dcpedit/mission-control/pcb/pcb.kicad_sch

## KiCad design pcb/pcb.kicad_sch (2024-04-23)

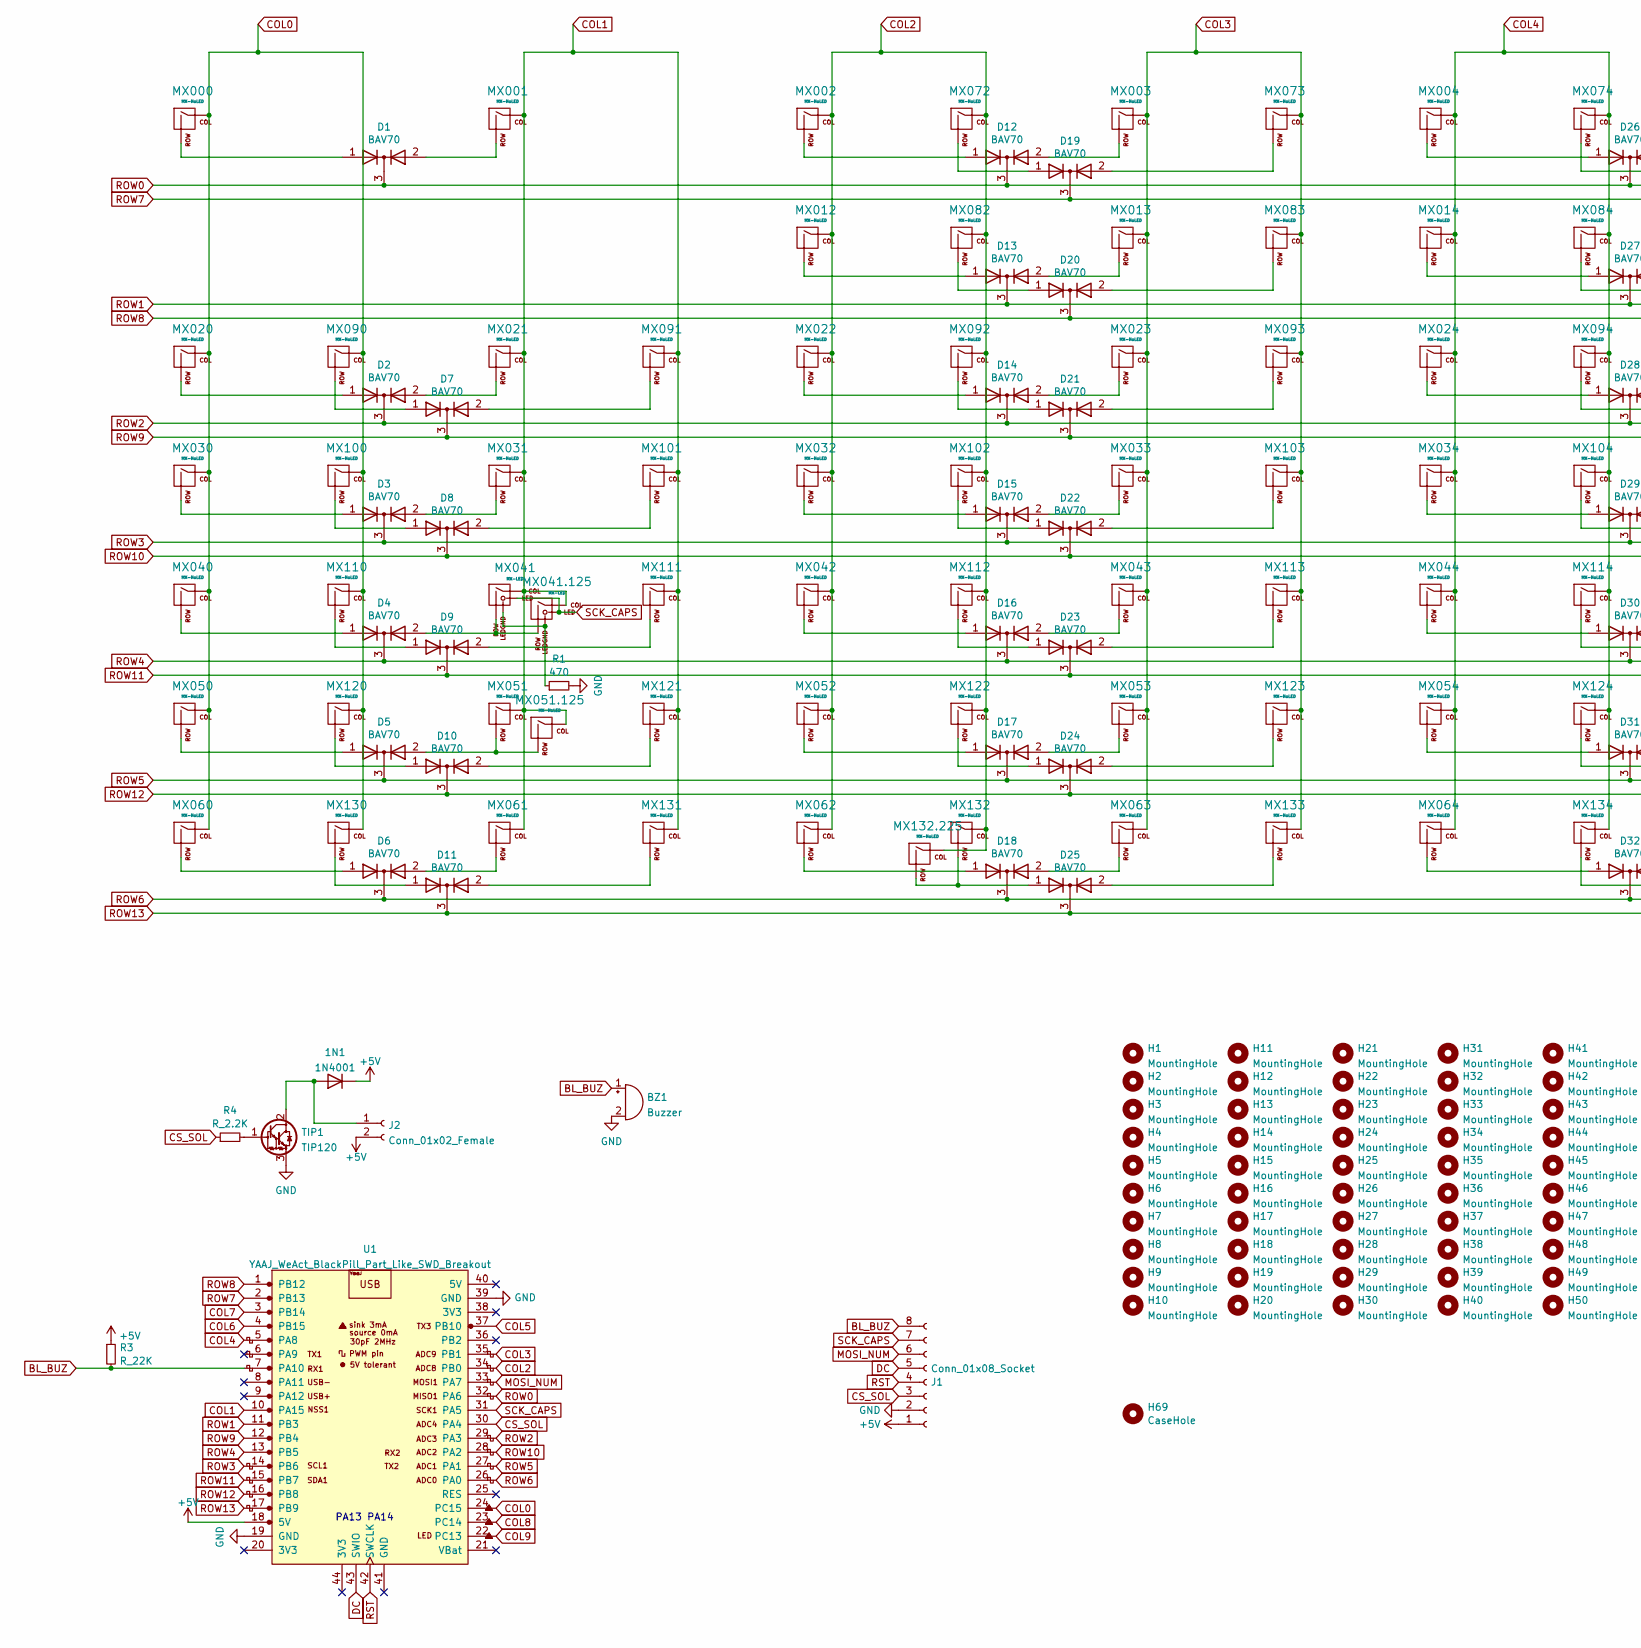
[picture p4: schematic pcb.kicad_sch, part in row 1, column 1]

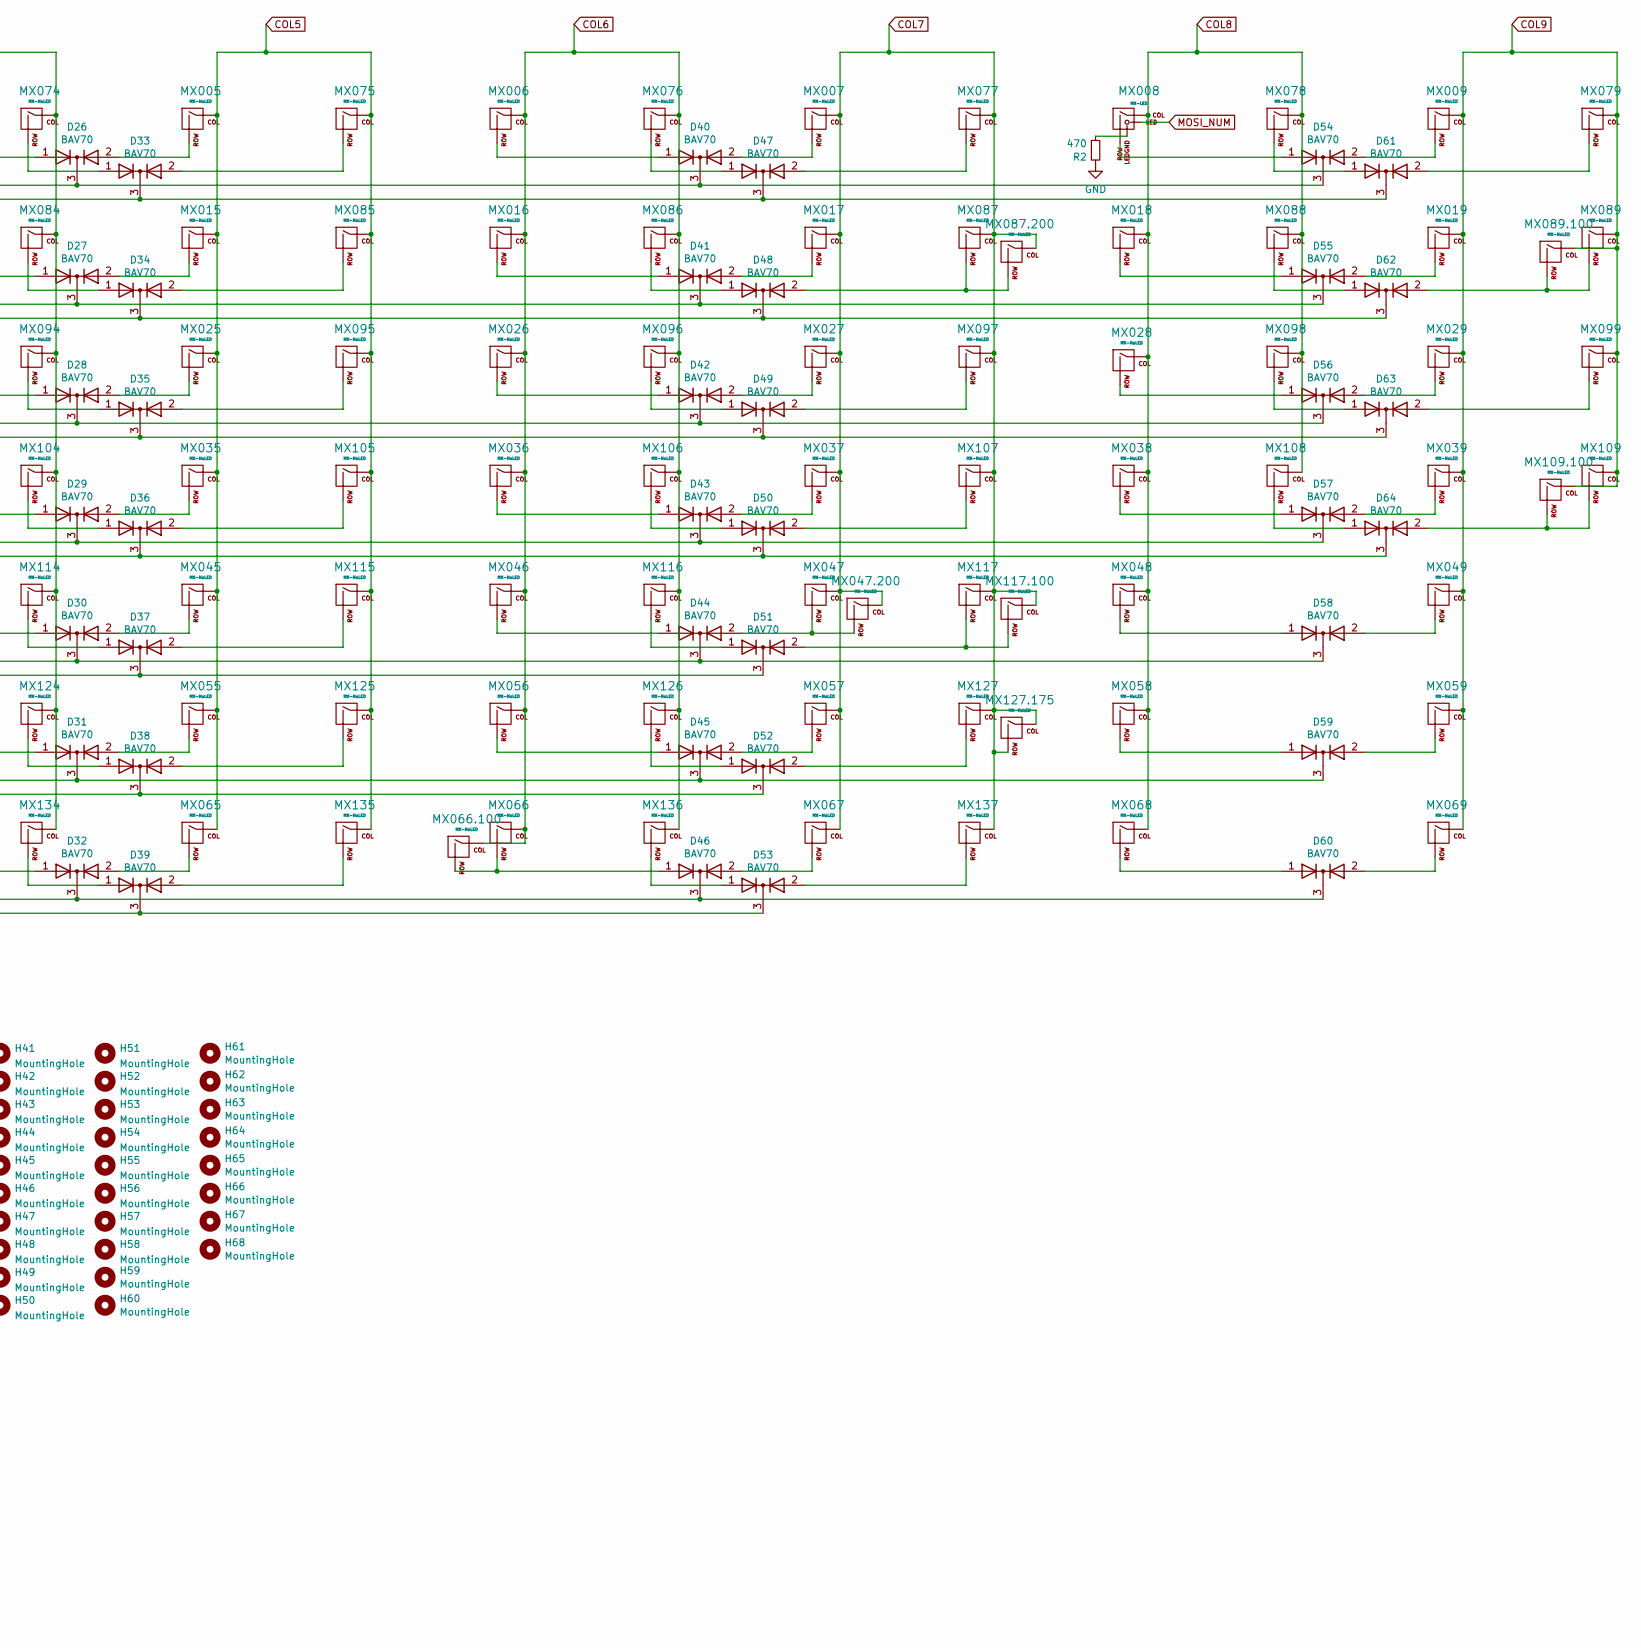
[picture p5: schematic pcb.kicad_sch, part in row 1, column 2]

Parts:
1N1: 1N4001; D_DO-41_SOD81_P10.16mm_Horizontal
BZ1: Buzzer
D1, D2, D3, D4, D5, D6, D7, D8, D9, D10, D11, D12, D13, D14, D15, D16, D17, D18, D19, D20, D21, D22, D23, D24, D25, D26, D27, D28, D29, D30, D31, D32, D33, D34, D35, D36, D37, D38, D39, D40, D41, D42, D43, D44, D45, D46, D47, D48, D49, D50, D51, D52, D53, D54, D55, D56, D57, D58, D59, D60, D61, D62, D63, D64: BAV70; SOT-23_Handsoldering
H1, H2, H3, H4, H5, H6, H7, H8, H9, H10, H11, H12, H13, H14, H15, H16, H17, H18, H19, H20, H21, H22, H23, H24, H25, H26, H27, H28, H29, H30, H31, H32, H33, H34, H35, H36, H37, H38, H39, H40, H41, H42, H43, H44, H45, H46, H47, H48, H49, H50, H51, H52, H53, H54, H55, H56, H57, H58, H59, H60, H61, H62, H63, H64, H65, H66, H67, H68: MountingHole
H69: CaseHole
J1: Conn_01x08_Socket
J2: Conn_01x02_Female; PinHeader_1x02_P2.54mm_Vertical
MX000, MX001, MX002, MX003, MX004, MX005, MX006, MX007, MX009, MX012, MX013, MX014, MX015, MX016, MX017, MX018, MX019, MX020, MX021, MX022, MX023, MX024, MX025, MX026, MX027, MX028, MX029, MX030, MX031, MX032, MX033, MX034, MX035, MX036, MX037, MX038, MX039, MX040, MX042, MX043, MX044, MX045, MX046, MX047, MX047.200, MX048, MX049, MX050, MX051, MX051.125, MX052, MX053, MX054, MX055, MX056, MX057, MX058, MX059, MX060, MX061, MX062, MX063, MX064, MX065, MX066, MX066.100, MX067, MX068, MX069, MX072, MX073, MX074, MX075, MX076, MX077, MX078, MX079, MX082, MX083, MX084, MX085, MX086, MX087, MX087.200, MX088, MX089, MX089.100, MX090, MX091, MX092, MX093, MX094, MX095, MX096, MX097, MX098, MX099, MX100, MX101, MX102, MX103, MX104, MX105, MX106, MX107, MX108, MX109, MX109.100, MX110, MX111, MX112, MX113, MX114, MX115, MX116, MX117, MX117.100, MX120, MX121, MX122, MX123, MX124, MX125, MX126, MX127, MX127.175, MX130, MX131, MX132, MX132.225, MX133, MX134, MX135, MX136, MX137: MX-NoLED; MXOnly-1U-NoLED
MX008, MX041, MX041.125: MX-LED
R1, R2: 470
R3: R_22K; Resistor
R4: R_2.2K; Resistor
TIP1: TIP120; TO-220-3_Vertical
U1: YAAJ_WeAct_BlackPill_Part_Like_SWD_Breakout; YAAJ_WeAct_BlackPill_SWD_2

Connections:
+5V: 1N1.1 (K), J1.1, J2.2, R3.1, U1.18 (5V)
BL_BUZ: BZ1.1 (-), J1.8, R3.2, U1.7 (PA10)
COL0: MX000.1 (COL), MX020.1 (COL), MX030.1 (COL), MX040.1 (COL), MX050.1 (COL), MX060.1 (COL), MX090.1 (COL), MX100.1 (COL), MX110.1 (COL), MX120.1 (COL), MX130.1 (COL), U1.24 (PC15)
COL1: MX001.1 (COL), MX021.1 (COL), MX031.1 (COL), MX041.1 (COL), MX041.125.1 (COL), MX051.1 (COL), MX051.125.1 (COL), MX061.1 (COL), MX091.1 (COL), MX101.1 (COL), MX111.1 (COL), MX121.1 (COL), MX131.1 (COL), U1.10 (PA15)
COL2: MX002.1 (COL), MX012.1 (COL), MX022.1 (COL), MX032.1 (COL), MX042.1 (COL), MX052.1 (COL), MX062.1 (COL), MX072.1 (COL), MX082.1 (COL), MX092.1 (COL), MX102.1 (COL), MX112.1 (COL), MX122.1 (COL), MX132.1 (COL), MX132.225.1 (COL), U1.34 (PB0)
COL3: MX003.1 (COL), MX013.1 (COL), MX023.1 (COL), MX033.1 (COL), MX043.1 (COL), MX053.1 (COL), MX063.1 (COL), MX073.1 (COL), MX083.1 (COL), MX093.1 (COL), MX103.1 (COL), MX113.1 (COL), MX123.1 (COL), MX133.1 (COL), U1.35 (PB1)
COL4: MX004.1 (COL), MX014.1 (COL), MX024.1 (COL), MX034.1 (COL), MX044.1 (COL), MX054.1 (COL), MX064.1 (COL), MX074.1 (COL), MX084.1 (COL), MX094.1 (COL), MX104.1 (COL), MX114.1 (COL), MX124.1 (COL), MX134.1 (COL), U1.5 (PA8)
COL5: MX005.1 (COL), MX015.1 (COL), MX025.1 (COL), MX035.1 (COL), MX045.1 (COL), MX055.1 (COL), MX065.1 (COL), MX075.1 (COL), MX085.1 (COL), MX095.1 (COL), MX105.1 (COL), MX115.1 (COL), MX125.1 (COL), MX135.1 (COL), U1.37 (PB10)
COL6: MX006.1 (COL), MX016.1 (COL), MX026.1 (COL), MX036.1 (COL), MX046.1 (COL), MX056.1 (COL), MX066.1 (COL), MX066.100.1 (COL), MX076.1 (COL), MX086.1 (COL), MX096.1 (COL), MX106.1 (COL), MX116.1 (COL), MX126.1 (COL), MX136.1 (COL), U1.4 (PB15)
COL7: MX007.1 (COL), MX017.1 (COL), MX027.1 (COL), MX037.1 (COL), MX047.1 (COL), MX047.200.1 (COL), MX057.1 (COL), MX067.1 (COL), MX077.1 (COL), MX087.1 (COL), MX087.200.1 (COL), MX097.1 (COL), MX107.1 (COL), MX117.1 (COL), MX117.100.1 (COL), MX127.1 (COL), MX127.175.1 (COL), MX127.175.2 (ROW), MX137.1 (COL), U1.3 (PB14)
COL8: MX008.1 (COL), MX018.1 (COL), MX028.1 (COL), MX038.1 (COL), MX048.1 (COL), MX058.1 (COL), MX068.1 (COL), MX078.1 (COL), MX088.1 (COL), MX098.1 (COL), MX108.1 (COL), U1.23 (PC14)
COL9: MX009.1 (COL), MX019.1 (COL), MX029.1 (COL), MX039.1 (COL), MX049.1 (COL), MX059.1 (COL), MX069.1 (COL), MX079.1 (COL), MX089.1 (COL), MX089.100.1 (COL), MX099.1 (COL), MX109.1 (COL), MX109.100.1 (COL), U1.22 (PC13)
CS_SOL: J1.3, R4.1, U1.30 (PA4)
DC: J1.5, U1.43 (SWIO)
GND: BZ1.2 (+), J1.2, R1.2, R2.2, TIP1.3 (E), U1.19 (GND), U1.39 (GND)
MOSI_NUM: J1.6, MX008.3 (LED), U1.33 (PA7)
unnamed: 1N1.2 (A), J2.1, TIP1.2 (C)
unnamed: D1.1 (A), MX000.2 (ROW)
unnamed: D1.2 (A), MX001.2 (ROW)
unnamed: D2.1 (A), MX020.2 (ROW)
unnamed: D2.2 (A), MX021.2 (ROW)
unnamed: D3.1 (A), MX030.2 (ROW)
unnamed: D3.2 (A), MX031.2 (ROW)
unnamed: D4.1 (A), MX040.2 (ROW)
unnamed: D4.2 (A), MX041.2 (ROW), MX041.125.2 (ROW)
unnamed: D5.1 (A), MX050.2 (ROW)
unnamed: D5.2 (A), MX051.2 (ROW), MX051.125.2 (ROW)
unnamed: D6.1 (A), MX060.2 (ROW)
unnamed: D6.2 (A), MX061.2 (ROW)
unnamed: D7.1 (A), MX090.2 (ROW)
unnamed: D7.2 (A), MX091.2 (ROW)
unnamed: D8.1 (A), MX100.2 (ROW)
unnamed: D8.2 (A), MX101.2 (ROW)
unnamed: D9.1 (A), MX110.2 (ROW)
unnamed: D9.2 (A), MX111.2 (ROW)
unnamed: D10.1 (A), MX120.2 (ROW)
unnamed: D10.2 (A), MX121.2 (ROW)
unnamed: D11.1 (A), MX130.2 (ROW)
unnamed: D11.2 (A), MX131.2 (ROW)
unnamed: D12.1 (A), MX002.2 (ROW)
unnamed: D12.2 (A), MX003.2 (ROW)
unnamed: D13.1 (A), MX012.2 (ROW)
unnamed: D13.2 (A), MX013.2 (ROW)
unnamed: D14.1 (A), MX022.2 (ROW)
unnamed: D14.2 (A), MX023.2 (ROW)
unnamed: D15.1 (A), MX032.2 (ROW)
unnamed: D15.2 (A), MX033.2 (ROW)
unnamed: D16.1 (A), MX042.2 (ROW)
unnamed: D16.2 (A), MX043.2 (ROW)
unnamed: D17.1 (A), MX052.2 (ROW)
unnamed: D17.2 (A), MX053.2 (ROW)
unnamed: D18.1 (A), MX062.2 (ROW)
unnamed: D18.2 (A), MX063.2 (ROW)
unnamed: D19.1 (A), MX072.2 (ROW)
unnamed: D19.2 (A), MX073.2 (ROW)
unnamed: D20.1 (A), MX082.2 (ROW)
unnamed: D20.2 (A), MX083.2 (ROW)
unnamed: D21.1 (A), MX092.2 (ROW)
unnamed: D21.2 (A), MX093.2 (ROW)
unnamed: D22.1 (A), MX102.2 (ROW)
unnamed: D22.2 (A), MX103.2 (ROW)
unnamed: D23.1 (A), MX112.2 (ROW)
unnamed: D23.2 (A), MX113.2 (ROW)
unnamed: D24.1 (A), MX122.2 (ROW)
unnamed: D24.2 (A), MX123.2 (ROW)
unnamed: D25.1 (A), MX132.2 (ROW), MX132.225.2 (ROW)
unnamed: D25.2 (A), MX133.2 (ROW)
unnamed: D26.1 (A), MX004.2 (ROW)
unnamed: D26.2 (A), MX005.2 (ROW)
unnamed: D27.1 (A), MX014.2 (ROW)
unnamed: D27.2 (A), MX015.2 (ROW)
unnamed: D28.1 (A), MX024.2 (ROW)
unnamed: D28.2 (A), MX025.2 (ROW)
unnamed: D29.1 (A), MX034.2 (ROW)
unnamed: D29.2 (A), MX035.2 (ROW)
unnamed: D30.1 (A), MX044.2 (ROW)
unnamed: D30.2 (A), MX045.2 (ROW)
unnamed: D31.1 (A), MX054.2 (ROW)
unnamed: D31.2 (A), MX055.2 (ROW)
unnamed: D32.1 (A), MX064.2 (ROW)
unnamed: D32.2 (A), MX065.2 (ROW)
unnamed: D33.1 (A), MX074.2 (ROW)
unnamed: D33.2 (A), MX075.2 (ROW)
unnamed: D34.1 (A), MX084.2 (ROW)
unnamed: D34.2 (A), MX085.2 (ROW)
unnamed: D35.1 (A), MX094.2 (ROW)
unnamed: D35.2 (A), MX095.2 (ROW)
unnamed: D36.1 (A), MX104.2 (ROW)
unnamed: D36.2 (A), MX105.2 (ROW)
unnamed: D37.1 (A), MX114.2 (ROW)
unnamed: D37.2 (A), MX115.2 (ROW)
unnamed: D38.1 (A), MX124.2 (ROW)
unnamed: D38.2 (A), MX125.2 (ROW)
unnamed: D39.1 (A), MX134.2 (ROW)
unnamed: D39.2 (A), MX135.2 (ROW)
unnamed: D40.1 (A), MX006.2 (ROW)
unnamed: D40.2 (A), MX007.2 (ROW)
unnamed: D41.1 (A), MX016.2 (ROW)
unnamed: D41.2 (A), MX017.2 (ROW)
unnamed: D42.1 (A), MX026.2 (ROW)
unnamed: D42.2 (A), MX027.2 (ROW)
unnamed: D43.1 (A), MX036.2 (ROW)
unnamed: D43.2 (A), MX037.2 (ROW)
unnamed: D44.1 (A), MX046.2 (ROW)
unnamed: D44.2 (A), MX047.2 (ROW), MX047.200.2 (ROW)
unnamed: D45.1 (A), MX056.2 (ROW)
unnamed: D45.2 (A), MX057.2 (ROW)
unnamed: D46.1 (A), MX066.2 (ROW), MX066.100.2 (ROW)
unnamed: D46.2 (A), MX067.2 (ROW)
unnamed: D47.1 (A), MX076.2 (ROW)
unnamed: D47.2 (A), MX077.2 (ROW)
unnamed: D48.1 (A), MX086.2 (ROW)
unnamed: D48.2 (A), MX087.2 (ROW), MX087.200.2 (ROW)
unnamed: D49.1 (A), MX096.2 (ROW)
unnamed: D49.2 (A), MX097.2 (ROW)
unnamed: D50.1 (A), MX106.2 (ROW)
unnamed: D50.2 (A), MX107.2 (ROW)
unnamed: D51.1 (A), MX116.2 (ROW)
unnamed: D51.2 (A), MX117.2 (ROW), MX117.100.2 (ROW)
unnamed: D52.1 (A), MX126.2 (ROW)
unnamed: D52.2 (A), MX127.2 (ROW)
unnamed: D53.1 (A), MX136.2 (ROW)
unnamed: D53.2 (A), MX137.2 (ROW)
unnamed: D54.1 (A), MX008.2 (ROW)
unnamed: D54.2 (A), MX009.2 (ROW)
unnamed: D55.1 (A), MX018.2 (ROW)
unnamed: D55.2 (A), MX019.2 (ROW)
unnamed: D56.1 (A), MX028.2 (ROW)
unnamed: D56.2 (A), MX029.2 (ROW)
unnamed: D57.1 (A), MX038.2 (ROW)
unnamed: D57.2 (A), MX039.2 (ROW)
unnamed: D58.1 (A), MX048.2 (ROW)
unnamed: D58.2 (A), MX049.2 (ROW)
unnamed: D59.1 (A), MX058.2 (ROW)
unnamed: D59.2 (A), MX059.2 (ROW)
unnamed: D60.1 (A), MX068.2 (ROW)
unnamed: D60.2 (A), MX069.2 (ROW)
unnamed: D61.1 (A), MX078.2 (ROW)
unnamed: D61.2 (A), MX079.2 (ROW)
unnamed: D62.1 (A), MX088.2 (ROW)
unnamed: D62.2 (A), MX089.2 (ROW), MX089.100.2 (ROW)
unnamed: D63.1 (A), MX098.2 (ROW)
unnamed: D63.2 (A), MX099.2 (ROW)
unnamed: D64.1 (A), MX108.2 (ROW)
unnamed: D64.2 (A), MX109.2 (ROW), MX109.100.2 (ROW)
unnamed: MX008.4 (LEDGND), R2.1
unnamed: MX041.4 (LEDGND), MX041.125.4 (LEDGND), R1.1
unnamed: R4.2, TIP1.1 (B)
ROW0: D1.3 (K), D12.3 (K), D26.3 (K), D40.3 (K), D54.3 (K), U1.32 (PA6)
ROW1: D13.3 (K), D27.3 (K), D41.3 (K), D55.3 (K), U1.11 (PB3)
ROW2: D2.3 (K), D14.3 (K), D28.3 (K), D42.3 (K), D56.3 (K), U1.29 (PA3)
ROW3: D3.3 (K), D15.3 (K), D29.3 (K), D43.3 (K), D57.3 (K), U1.14 (PB6)
ROW4: D4.3 (K), D16.3 (K), D30.3 (K), D44.3 (K), D58.3 (K), U1.13 (PB5)
ROW5: D5.3 (K), D17.3 (K), D31.3 (K), D45.3 (K), D59.3 (K), U1.27 (PA1)
ROW6: D6.3 (K), D18.3 (K), D32.3 (K), D46.3 (K), D60.3 (K), U1.26 (PA0)
ROW7: D19.3 (K), D33.3 (K), D47.3 (K), D61.3 (K), U1.2 (PB13)
ROW8: D20.3 (K), D34.3 (K), D48.3 (K), D62.3 (K), U1.1 (PB12)
ROW9: D7.3 (K), D21.3 (K), D35.3 (K), D49.3 (K), D63.3 (K), U1.12 (PB4)
ROW10: D8.3 (K), D22.3 (K), D36.3 (K), D50.3 (K), D64.3 (K), U1.28 (PA2)
ROW11: D9.3 (K), D23.3 (K), D37.3 (K), D51.3 (K), U1.15 (PB7)
ROW12: D10.3 (K), D24.3 (K), D38.3 (K), D52.3 (K), U1.16 (PB8)
ROW13: D11.3 (K), D25.3 (K), D39.3 (K), D53.3 (K), U1.17 (PB9)
RST: J1.4, U1.42 (SWCLK)
SCK_CAPS: J1.7, MX041.3 (LED), MX041.125.3 (LED), U1.31 (PA5)

Notes on the sheet:
PA13 PA14
